Mircas001/AnaDash/hardware/case/assets/meterLabels_g3.png

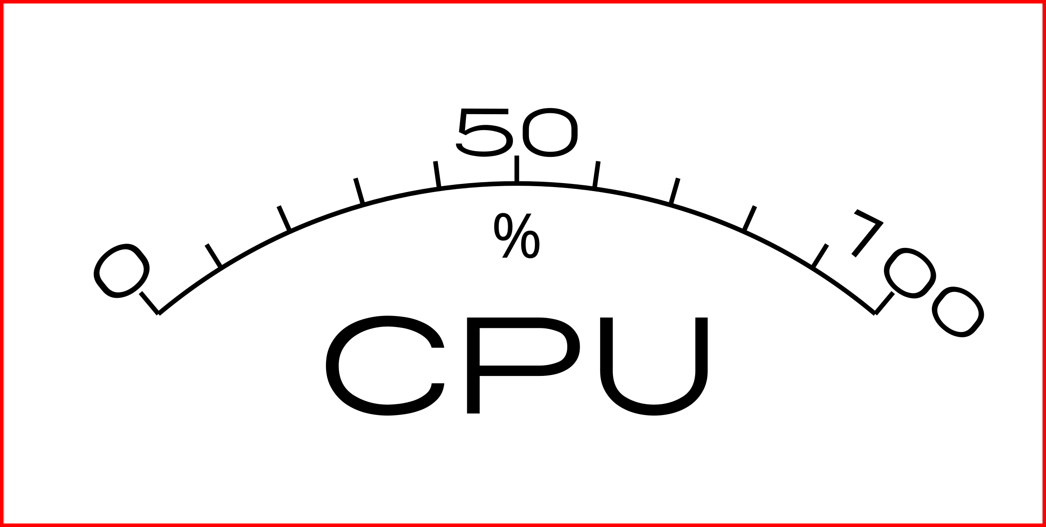
hardware/case/assets/meterLabels_g3.png
