Mircas001/AnaDash/pcb/anadash_pcb.kicad_sch

## KiCad design pcb/anadash_pcb.kicad_sch (2026-07-03)

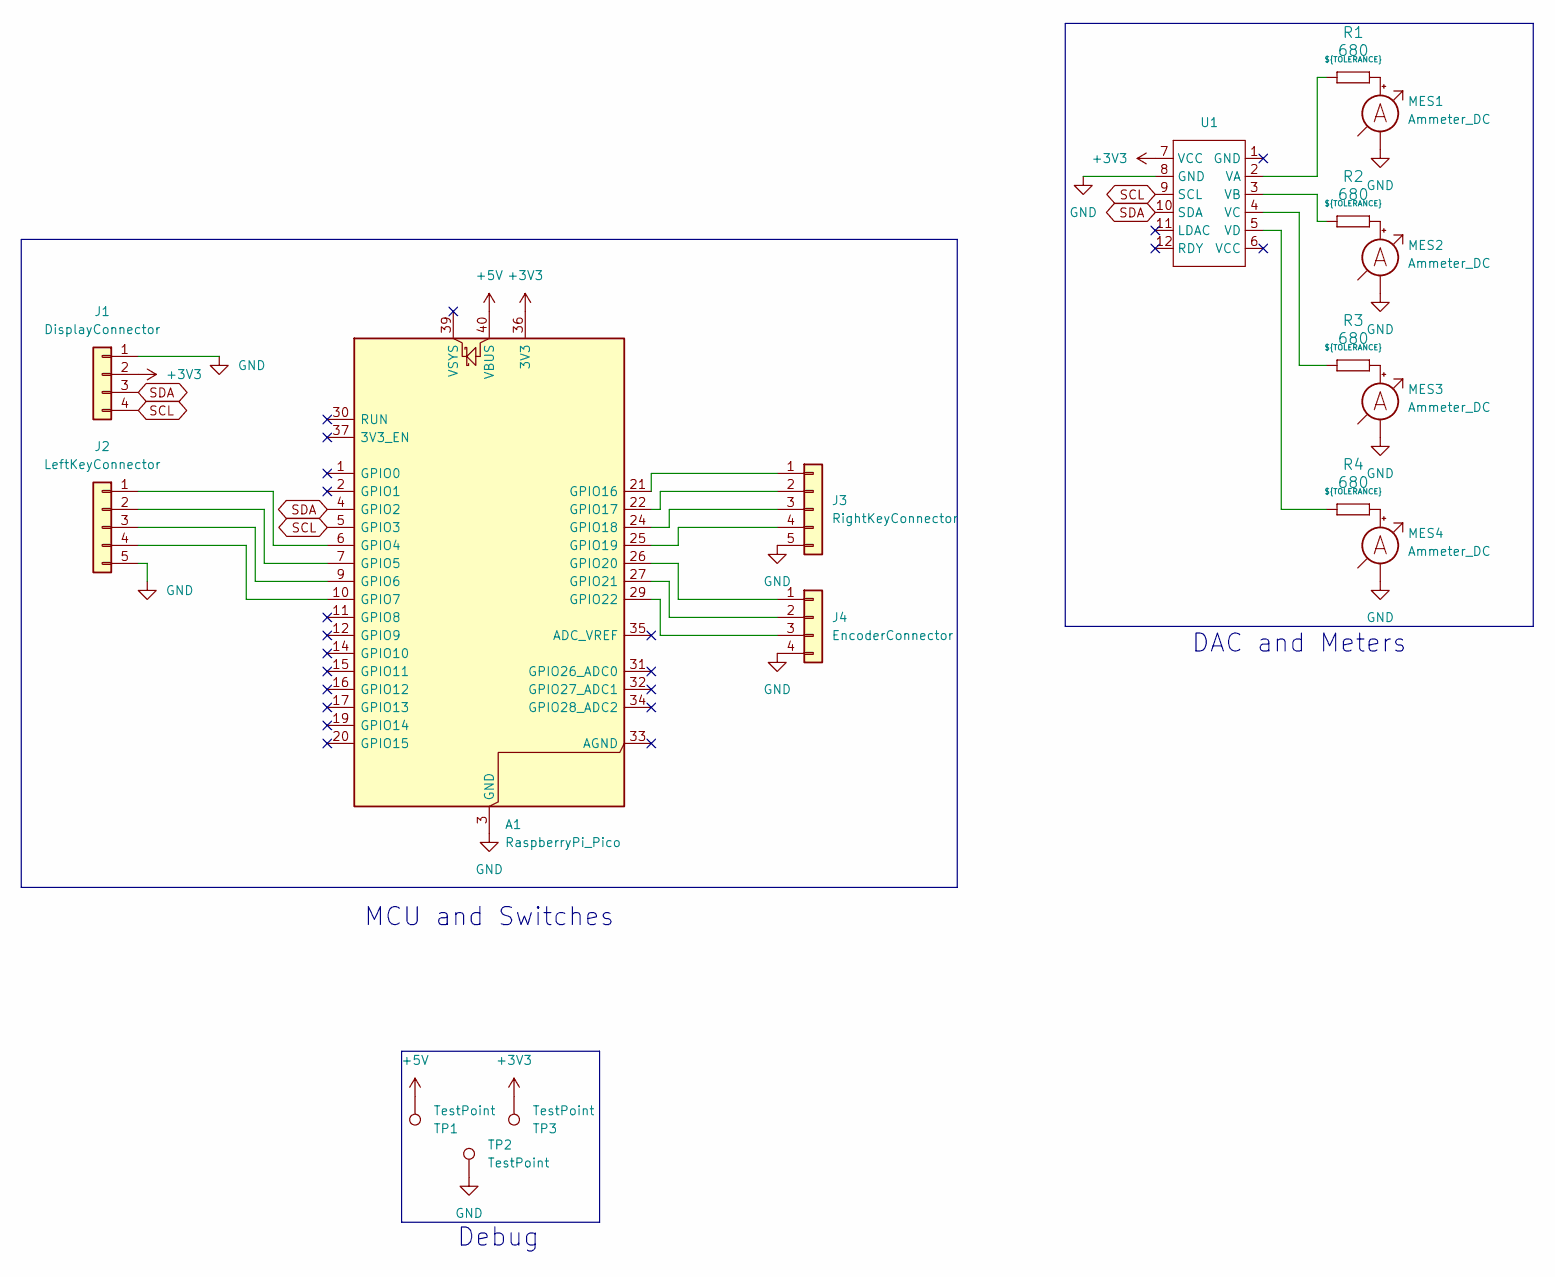
[picture p24: schematic anadash_pcb.kicad_sch]

Parts:
A1: RaspberryPi_Pico; RaspberryPi_Pico_Common_Unspecified
J1: DisplayConnector; JST_XH_B4B-XH-A_1x04_P2.50mm_Vertical
J2: LeftKeyConnector; JST_XH_B5B-XH-A_1x05_P2.50mm_Vertical
J3: RightKeyConnector; JST_XH_B5B-XH-A_1x05_P2.50mm_Vertical
J4: EncoderConnector; JST_XH_B4B-XH-A_1x04_P2.50mm_Vertical
MES1, MES2, MES3, MES4: Ammeter_DC; JST_XH_B2B-XH-A_1x02_P2.50mm_Vertical
R1, R2, R3, R4: 680; R_Axial_DIN0207_L6.3mm_D2.5mm_P7.62mm_Horizontal; Tolerance ${TOLERANCE}
TP1, TP2, TP3: TestPoint; TestPoint_Pad_D2.5mm
U1: Adafruit_MCP4728

Connections:
+3V3: A1.36 (3V3), J1.2, TP3.1, U1.7 (VCC)
+5V: A1.40 (VBUS), TP1.1
GND: A1.3 (GND), A1.8 (GND), A1.13 (GND), A1.18 (GND), A1.23 (GND), A1.28 (GND), A1.38 (GND), J1.1, J2.5, J3.5, J4.4, MES1.1 (-), MES2.1 (-), MES3.1 (-), MES4.1 (-), TP2.1, U1.8 (GND)
unnamed: A1.6 (GPIO4), J2.1
unnamed: A1.7 (GPIO5), J2.2
unnamed: A1.9 (GPIO6), J2.3
unnamed: A1.10 (GPIO7), J2.4
unnamed: A1.21 (GPIO16), J3.1
unnamed: A1.22 (GPIO17), J3.2
unnamed: A1.24 (GPIO18), J3.3
unnamed: A1.25 (GPIO19), J3.4
unnamed: A1.26 (GPIO20), J4.1
unnamed: A1.27 (GPIO21), J4.2
unnamed: A1.29 (GPIO22), J4.3
unnamed: MES1.2 (+), R1.2
unnamed: MES2.2 (+), R2.2
unnamed: MES3.2 (+), R3.2
unnamed: MES4.2 (+), R4.2
unnamed: R1.1, U1.2 (VA)
unnamed: R2.1, U1.3 (VB)
unnamed: R3.1, U1.4 (VC)
unnamed: R4.1, U1.5 (VD)
SCL: A1.5 (GPIO3), J1.4, U1.9 (SCL)
SDA: A1.4 (GPIO2), J1.3, U1.10 (SDA)

Notes on the sheet:
MCU and Switches
DAC and Meters
Debug
