Mircas001/AnaDash/pcb/switchesanddisplay.kicad_sch

## KiCad design pcb/switchesanddisplay.kicad_sch (2026-07-03)

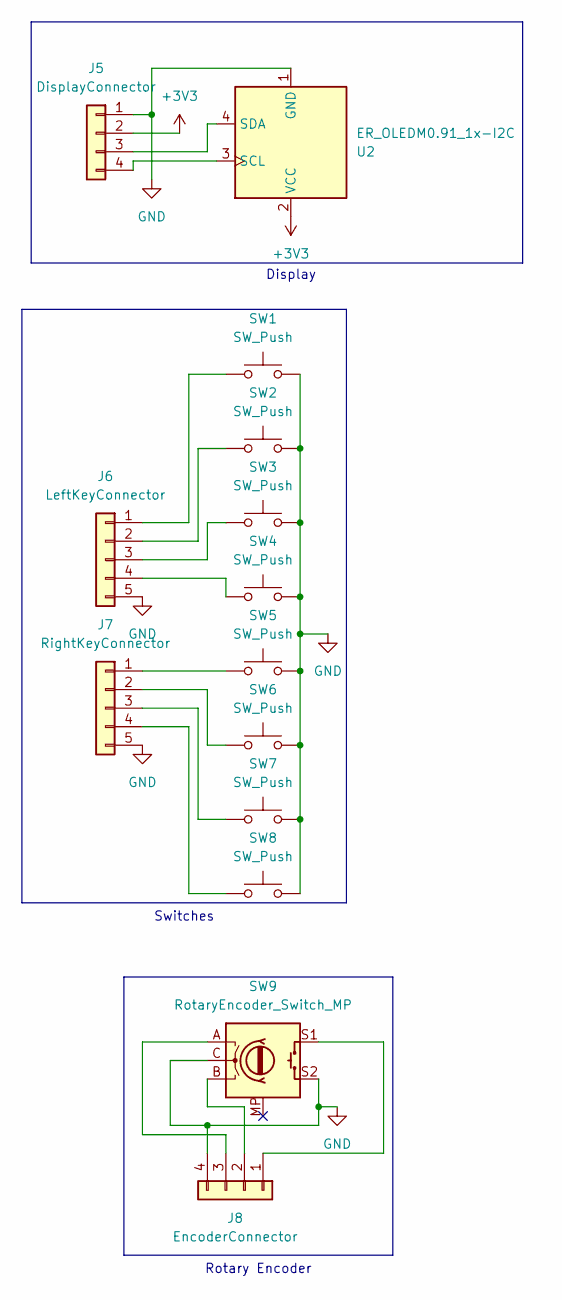
[picture p25: schematic switchesanddisplay.kicad_sch]

Parts:
J5: DisplayConnector; JST_XH_B4B-XH-A_1x04_P2.50mm_Vertical
J6: LeftKeyConnector; JST_XH_B5B-XH-A_1x05_P2.50mm_Vertical
J7: RightKeyConnector; JST_XH_B5B-XH-A_1x05_P2.50mm_Vertical
J8: EncoderConnector; JST_XH_B4B-XH-A_1x04_P2.50mm_Vertical
SW1, SW2, SW3, SW4, SW5, SW6, SW7, SW8: SW_Push; SW_Cherry_MX_1.00u_PCB
SW9: RotaryEncoder_Switch_MP; RotaryEncoder_Alps_EC11E-Switch_Vertical_H20mm
U2: ER_OLEDM0.91_1x-I2C; JST_XH_B4B-XH-A_1x04_P2.50mm_Vertical

Connections:
+3V3: J5.2, U2.2 (VCC)
GND: J5.1, J6.5, J7.5, J8.4, SW1.2, SW2.2, SW3.2, SW4.2, SW5.2, SW6.2, SW7.2, SW8.2, SW9.C, SW9.S2, U2.1 (GND)
unnamed: J5.3, U2.4 (SDA)
unnamed: J5.4, U2.3 (SCL)
unnamed: J6.1, SW1.1
unnamed: J6.2, SW2.1
unnamed: J6.3, SW3.1
unnamed: J6.4, SW4.1
unnamed: J7.1, SW5.1
unnamed: J7.2, SW6.1
unnamed: J7.3, SW7.1
unnamed: J7.4, SW8.1
unnamed: J8.1, SW9.S1
unnamed: J8.2, SW9.B
unnamed: J8.3, SW9.A

Notes on the sheet:
Display
Switches
Rotary Encoder
