Mircas001/AnaDash/software/anadash-driver/src/mpris_monitor.rs

use log::{info, warn};
use mpris::{Metadata, PlaybackStatus, Player, PlayerFinder};
use shared::PlayerStatus;
use std::time::Duration;

pub struct MprisPlayer {
    player: Option<Player>,
    pub artist: String,
    pub duration: u64,
    pub progress: u64,
    pub title: String,
    pub status: PlayerStatus,
}

impl MprisPlayer {
    pub fn new() -> Self {
        info!("Looking for mpris player");
        let player = PlayerFinder::new()
            .ok()
            .and_then(|finder| finder.find_active().ok());

        Self {
            player,
            artist: String::new(),
            duration: 0,
            progress: 0,
            title: String::new(),
            status: PlayerStatus::Stopped,
        }
    }

    fn try_reconnection(&mut self) {
        if let Ok(finder) = PlayerFinder::new() {
            // * if this goes ok, get on the block
            if let Ok(player) = finder.find_active() {
                // * if he gets an active player
                self.player = Some(player); // * make new player
            }
        }
    }

    fn get_time(duration: Option<Duration>) -> u64 {
        match duration {
            Some(duration) => duration.as_secs(),
            None => 0,
        }
    }

    fn get_artist(metadata: &Metadata) -> String {
        match metadata.artists() {
            Some(artists) if !artists.is_empty() => artists.join(" + "),
            _ => "Unknown artist".to_string(),
        }
    }

    fn get_title(metadata: &Metadata) -> String {
        metadata.title().unwrap_or("Unknown title").to_string()
    }

    fn get_playback_status(status: PlaybackStatus) -> PlayerStatus {
        match status {
            PlaybackStatus::Playing => PlayerStatus::Playing,
            PlaybackStatus::Paused => PlayerStatus::Paused,
            PlaybackStatus::Stopped => PlayerStatus::Stopped,
        }
    }

    pub fn update(&mut self) {
        let player = match &self.player {
            Some(player) => player,
            None => {
                warn!("Lost connection with the player");
                self.try_reconnection();
                match &self.player {
                    Some(player) => player,
                    None => {
                        self.artist.clear();
                        self.title = "No media".to_string();
                        self.duration = 0;
                        self.progress = 0;
                        self.status = PlayerStatus::Stopped;
                        return;
                    }
                }
            }
        };

        let metadata = match player.get_metadata() {
            Ok(metadata) => metadata,
            Err(_) => {
                self.player = None;
                return;
            }
        };

        let position = player.get_position().ok();
        let status = player
            .get_playback_status()
            .unwrap_or(PlaybackStatus::Stopped);

        self.artist = Self::get_artist(&metadata);
        self.title = Self::get_title(&metadata);
        self.duration = Self::get_time(metadata.length());
        self.progress = Self::get_time(position);
        self.status = Self::get_playback_status(status);
    }
}
